rahul0805/Stair_climber/Payload Box/payload_lid.SLDPRT

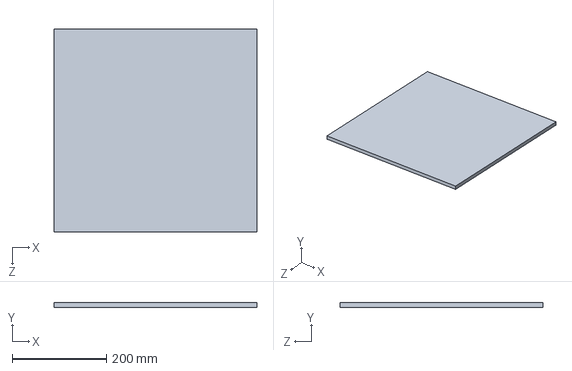
[picture p60: CAD file, 2020-08-08]
Payload Box/payload_lid.SLDPRT
430.0 x 10.0 x 430.0 mm
