rahul0805/Stair_climber/Tri Wheel/Casing/Carrier_tumble.SLDPRT

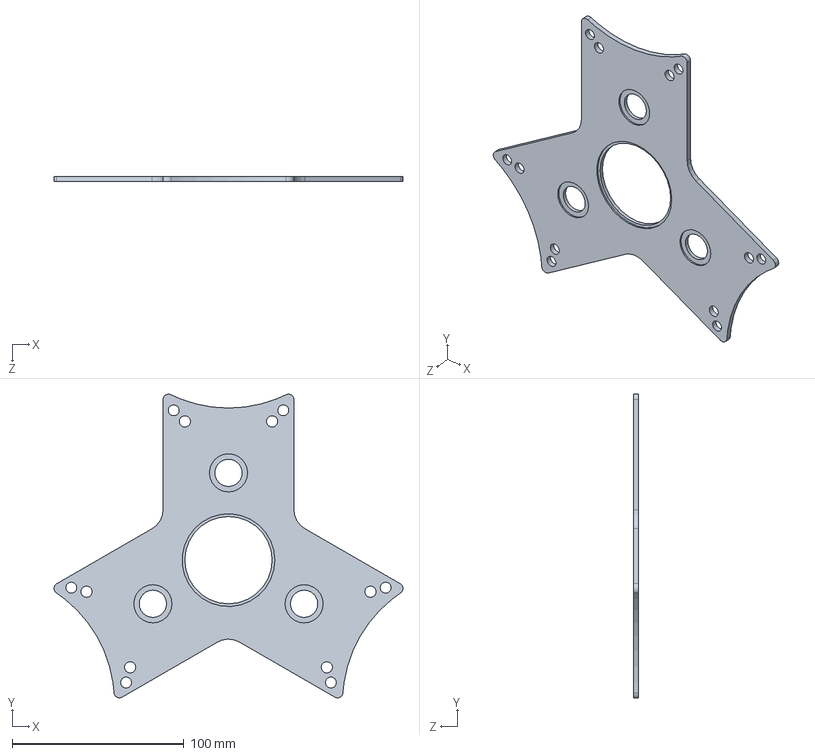
[picture p61: CAD file, 2020-08-08]
Tri Wheel/Casing/Carrier_tumble.SLDPRT
203.1 x 176.7 x 3.17 mm
