rahul0805/Stair_climber/Tri Wheel/Gears/Central & idler gears.SLDPRT

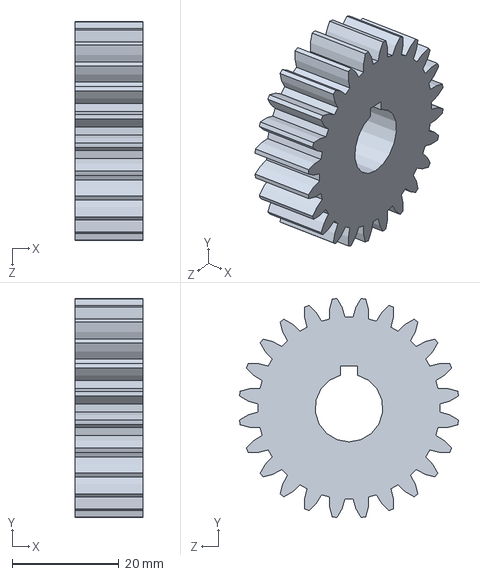
[picture p62: CAD file, 2020-08-08]
Tri Wheel/Gears/Central & idler gears.SLDPRT
12.7 x 41.0 x 41.0 mm
