rahul0805/Stair_climber/Tri Wheel/Shafts/Shaft C.SLDPRT

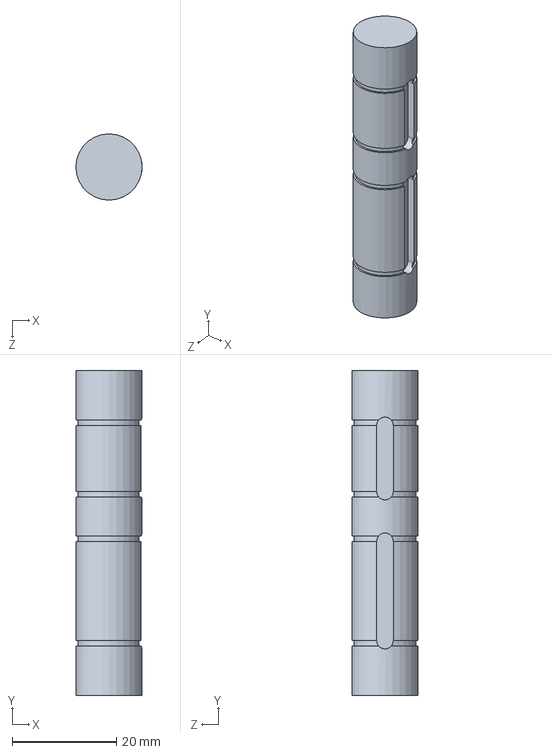
[picture p63: CAD file, 2020-08-08]
Tri Wheel/Shafts/Shaft C.SLDPRT
12.7 x 62.3 x 12.7 mm
