rahul0805/Stair_climber/Gimbal/Gimbal.stp

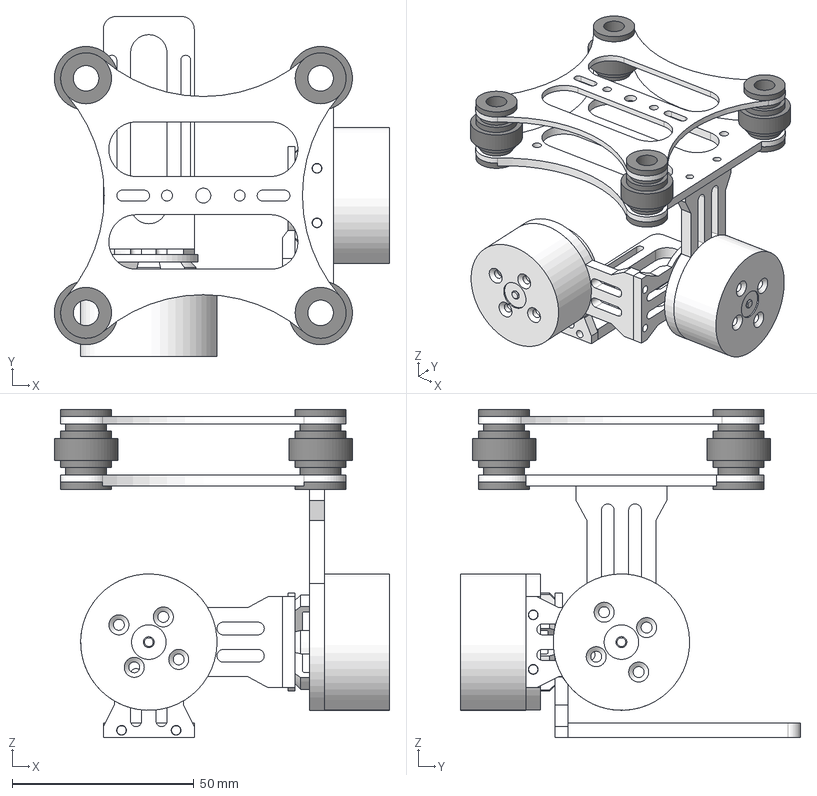
[picture p64: CAD file, 2020-08-08]
Gimbal/Gimbal.stp
92.3 x 93.5 x 90.3 mm
Top Support Plate
Rubber Spacers x 4
Bottom Support Plate
Roll Bracket
Motor
Motor Bracket x 2
Pitch Bracket
Motor - OH
Camera Support
