rahul0805/Stair_climber/Motor Assembly/midd.SLDPRT

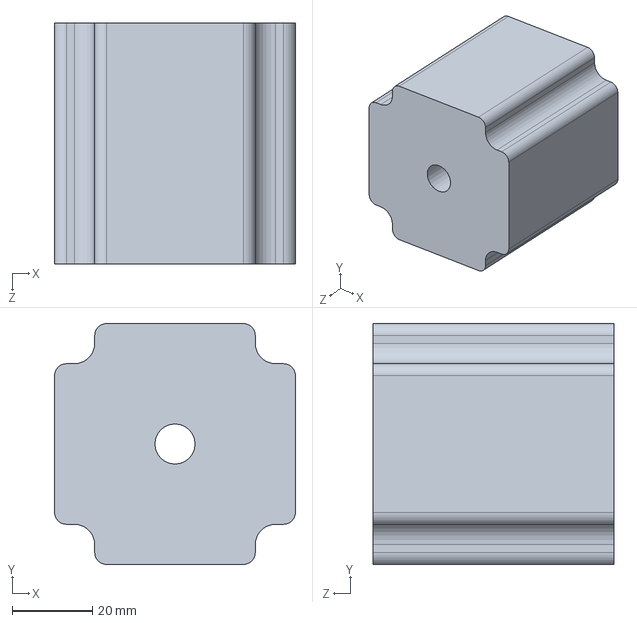
[picture p65: CAD file, 2020-08-08]
Motor Assembly/midd.SLDPRT
60.0 x 60.0 x 60.0 mm
