rahul0805/Stair_climber/Payload Box/payload_bottom.SLDPRT

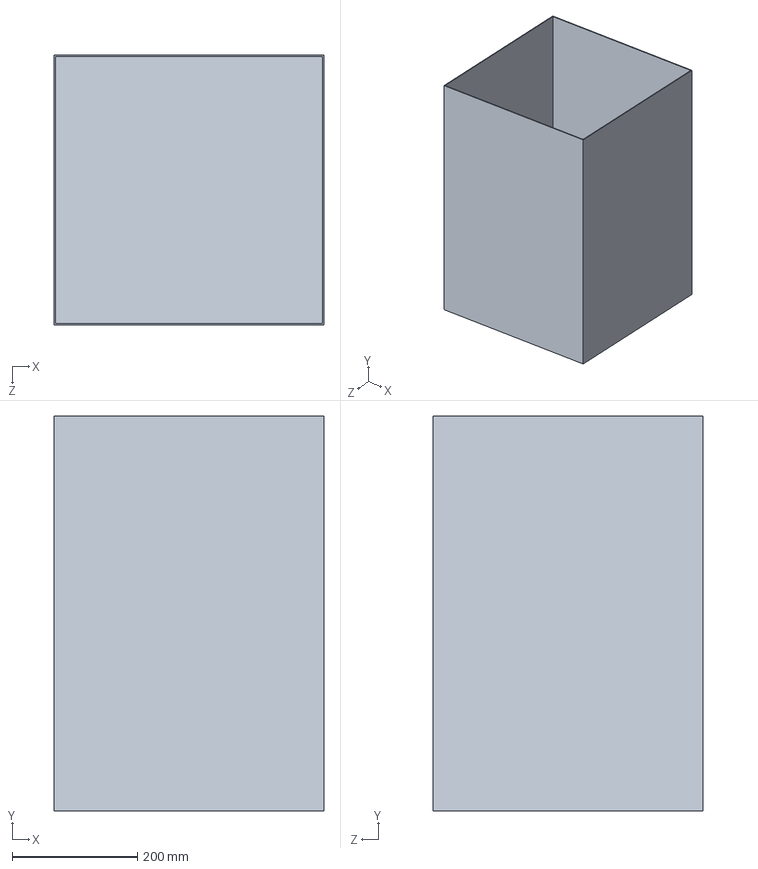
[picture p66: CAD file, 2020-08-08]
Payload Box/payload_bottom.SLDPRT
430.0 x 630.0 x 430.0 mm
