rahul0805/Stair_climber/Tri Wheel/Casing/Carrier_Drive Plate.SLDPRT

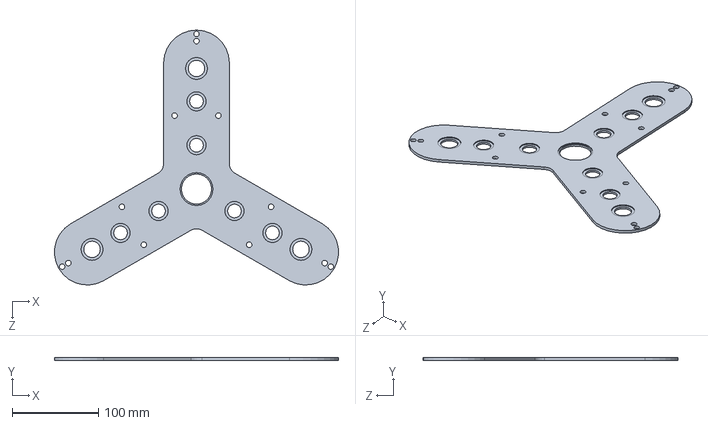
[picture p67: CAD file, 2020-08-08]
Tri Wheel/Casing/Carrier_Drive Plate.SLDPRT
329.0 x 3.17 x 295.2 mm
