rahul0805/Stair_climber/Tri Wheel/Shafts/Shaft D2.SLDPRT

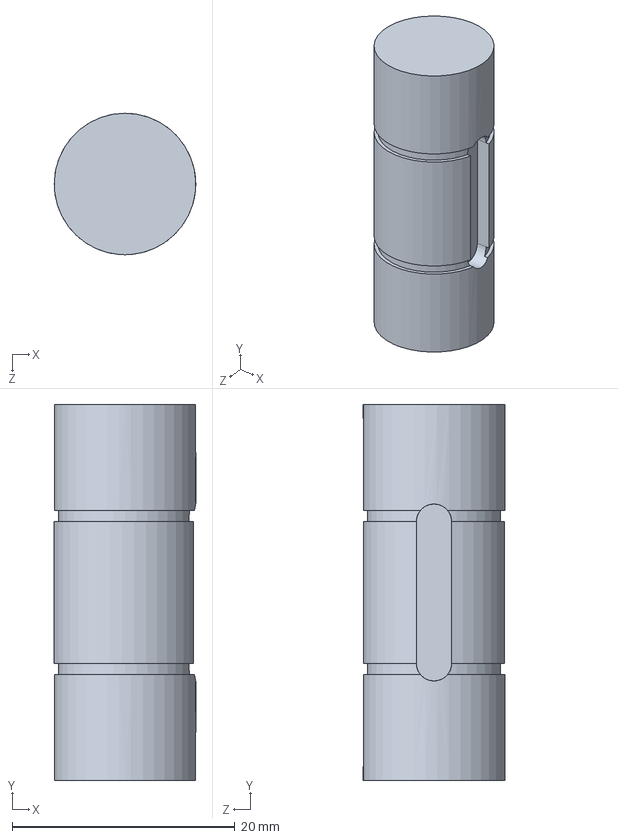
[picture p68: CAD file, 2020-08-08]
Tri Wheel/Shafts/Shaft D2.SLDPRT
12.7 x 33.7 x 12.7 mm
