rahul0805/Stair_climber/Tri Wheel/Wheels/wheel.SLDPRT

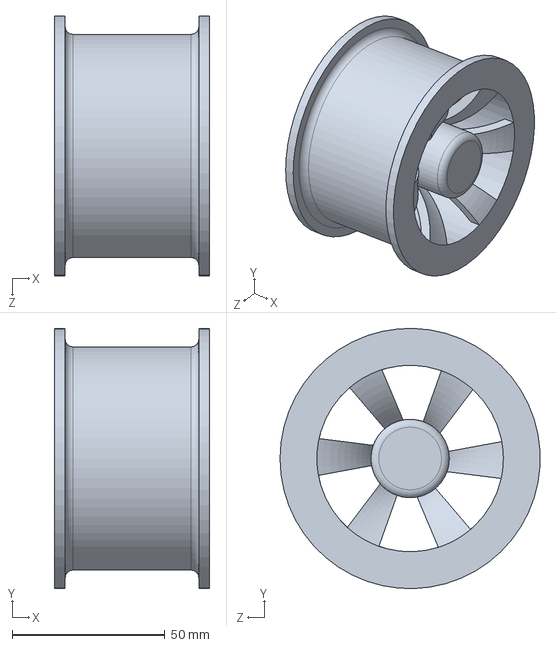
[picture p69: CAD file, 2020-08-08]
Tri Wheel/Wheels/wheel.SLDPRT
50.8 x 85.0 x 85.0 mm
