rahul0805/Stair_climber/Linear Actuator/HDA-STROKE.SLDPRT

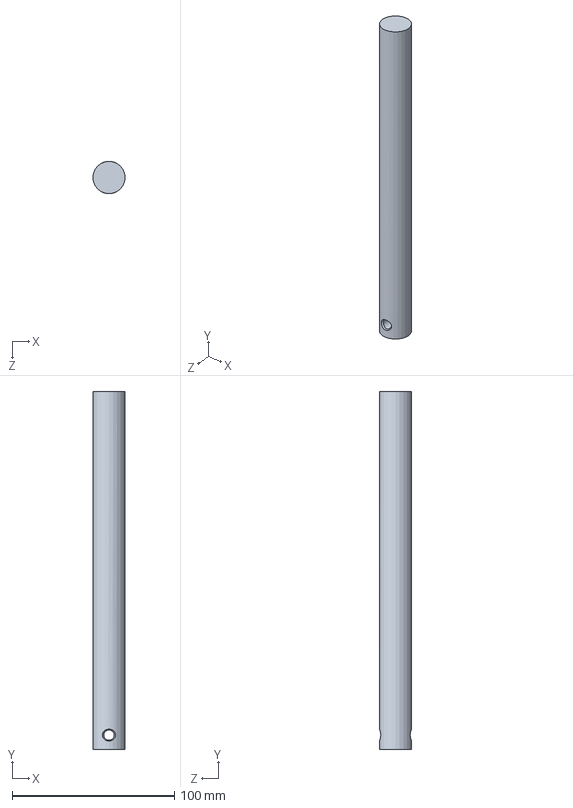
[picture p70: CAD file, 2020-08-08]
Linear Actuator/HDA-STROKE.SLDPRT
19.9 x 221.0 x 19.9 mm
