rahul0805/Stair_climber/Motor Assembly/last one.SLDPRT

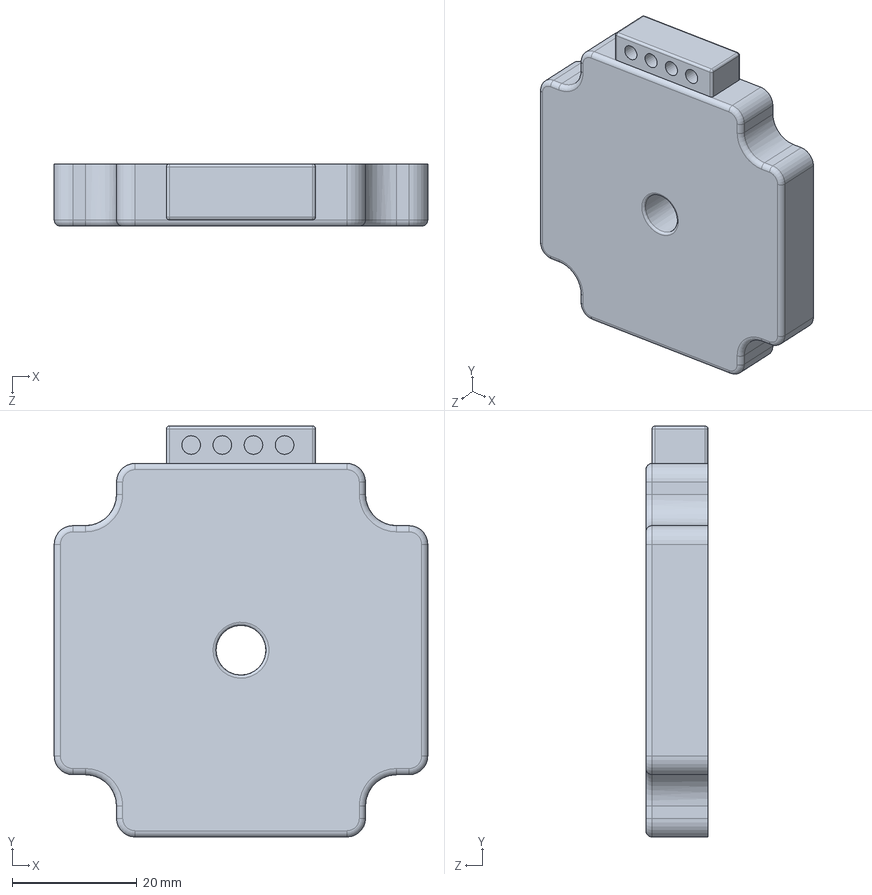
[picture p71: CAD file, 2020-08-08]
Motor Assembly/last one.SLDPRT
60.0 x 66.0 x 10.0 mm
