rahul0805/Stair_climber/Tri Wheel/Gears/Large Driving Gears.SLDPRT

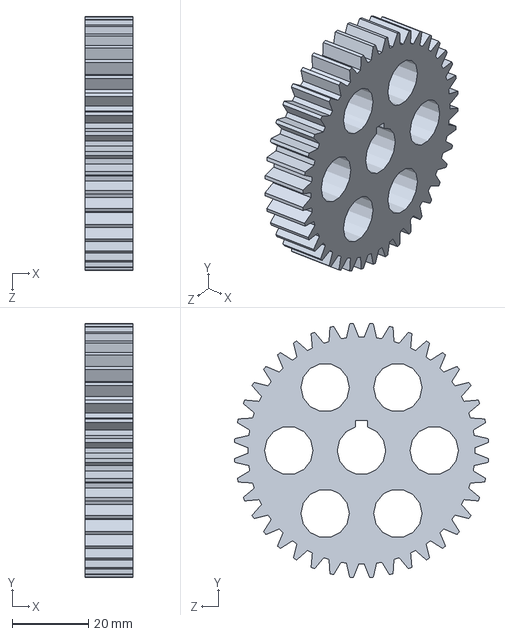
[picture p72: CAD file, 2020-08-08]
Tri Wheel/Gears/Large Driving Gears.SLDPRT
12.7 x 66.5 x 66.5 mm
