rahul0805/Stair_climber/Tri Wheel/Shafts/Shaft A.SLDPRT

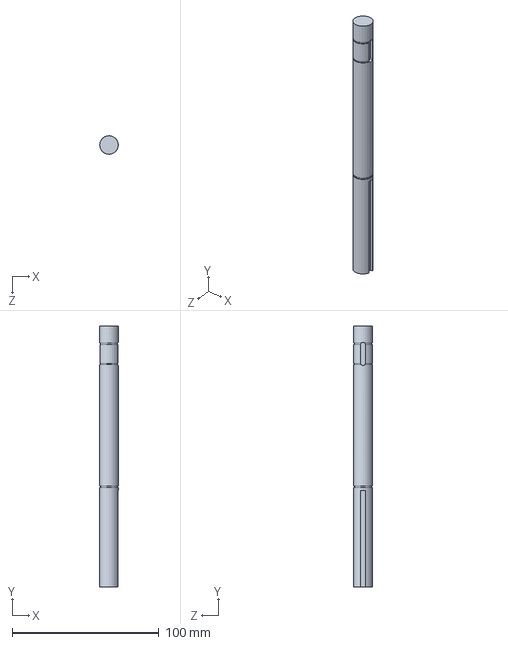
[picture p73: CAD file, 2020-08-08]
Tri Wheel/Shafts/Shaft A.SLDPRT
12.7 x 177.8 x 12.7 mm
