rahul0805/Stair_climber/Motor Assembly/one.SLDPRT

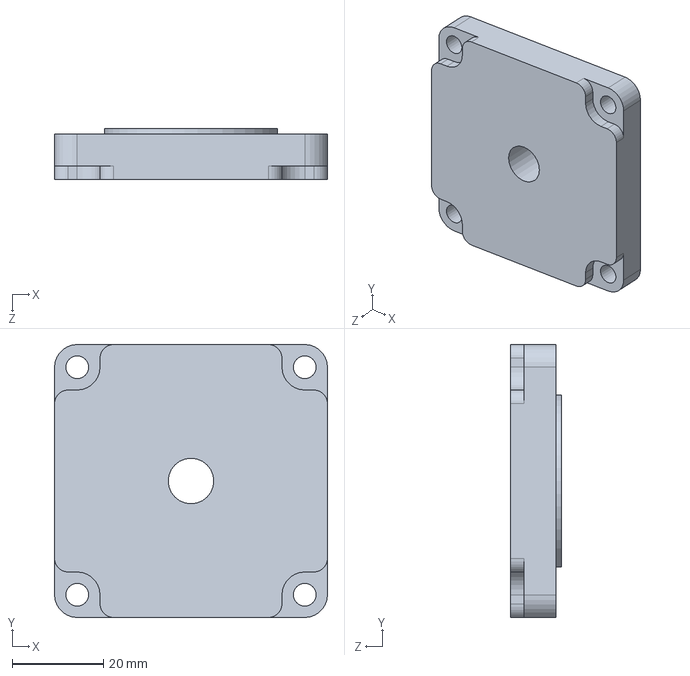
[picture p74: CAD file, 2020-08-08]
Motor Assembly/one.SLDPRT
60.0 x 60.0 x 11.2 mm
