rahul0805/Stair_climber/Tri Wheel/Gears/Small Tumbling Gears.SLDPRT

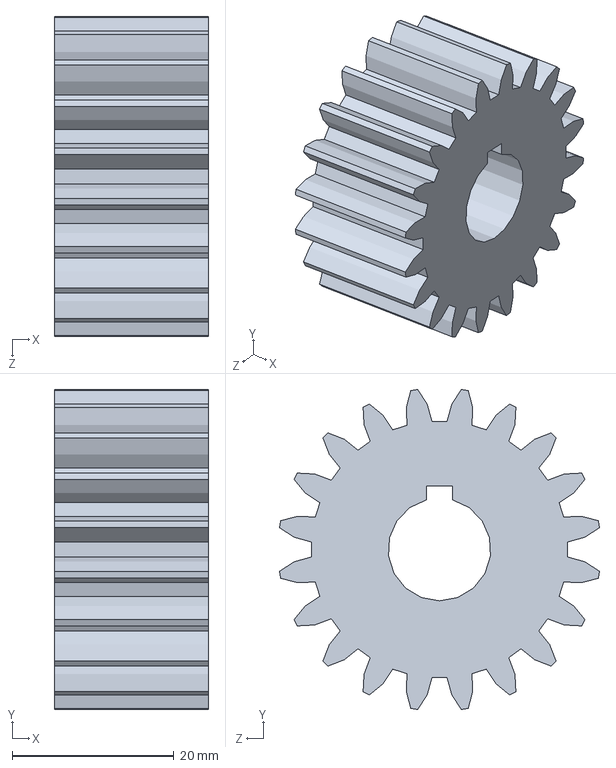
[picture p75: CAD file, 2020-08-08]
Tri Wheel/Gears/Small Tumbling Gears.SLDPRT
19.1 x 39.6 x 39.6 mm
