rahul0805/Stair_climber/Linear Actuator/HDA-SHROUD-CAP.SLDPRT

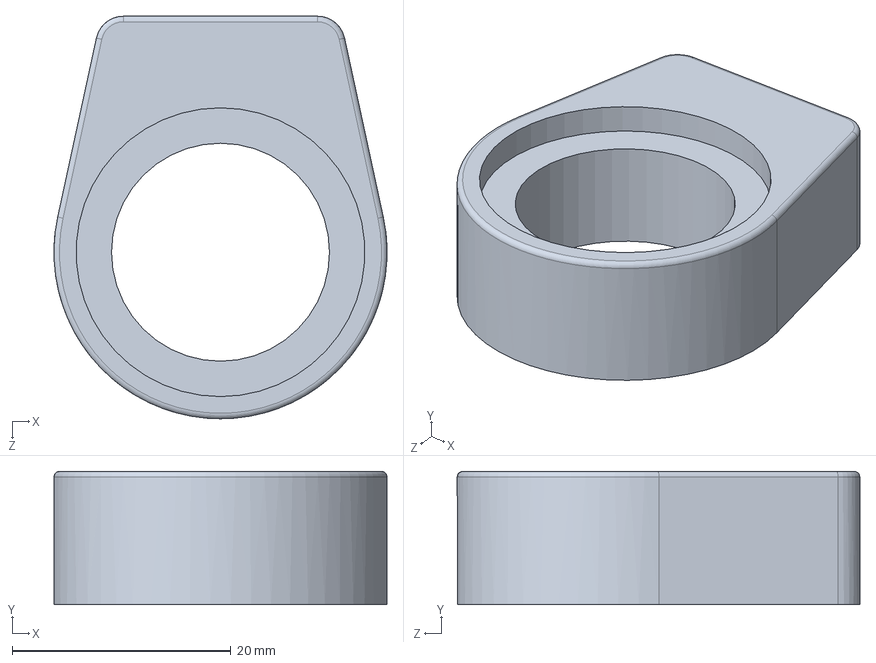
[picture p76: CAD file, 2020-08-08]
Linear Actuator/HDA-SHROUD-CAP.SLDPRT
30.5 x 12.2 x 36.8 mm
