rahul0805/Stair_climber/Linear Actuator/HDA-SHROUD.SLDPRT

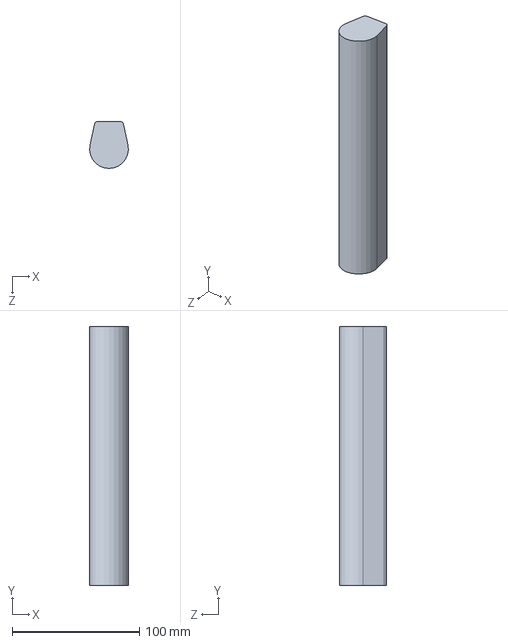
[picture p77: CAD file, 2020-08-08]
Linear Actuator/HDA-SHROUD.SLDPRT
30.5 x 203.2 x 36.8 mm
