rahul0805/Stair_climber/Linear Actuator/_test - w-celvis.STEP

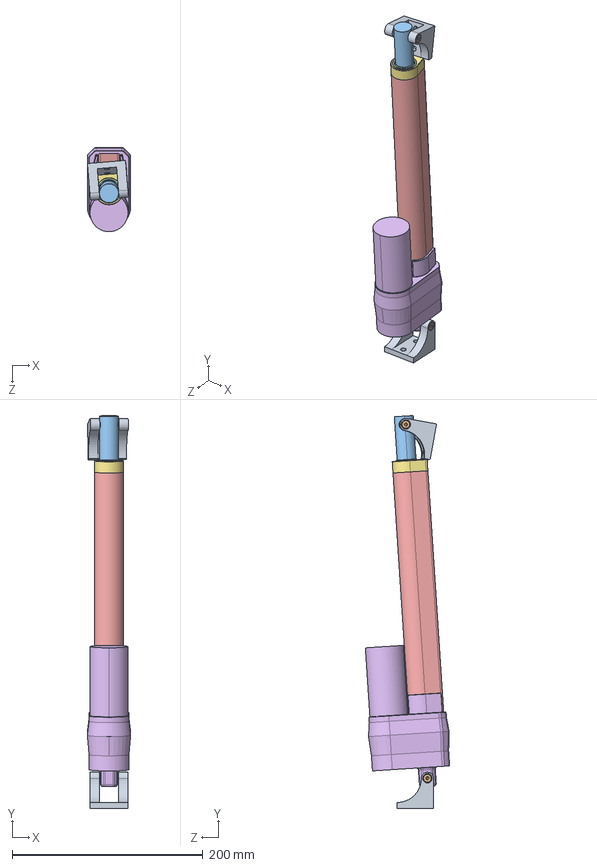
[picture p78: CAD file, 2020-08-08]
Linear Actuator/_test - w-celvis.STEP
45.5 x 412.5 x 88.5 mm
HDA Clevis Mount x 2
Shoulder Bolt .25 x 1 - 10-24_SHSSCREW 0.25x1-N x 2
HDA-STROKE_8IN
HDA-CAP-SEAL
HDA-SHROUD_8IN
HDA-BASE
HDA-SHROUD-CAP
