rahul0805/Stair_climber/Linear Actuator/HDA-BASE.SLDPRT

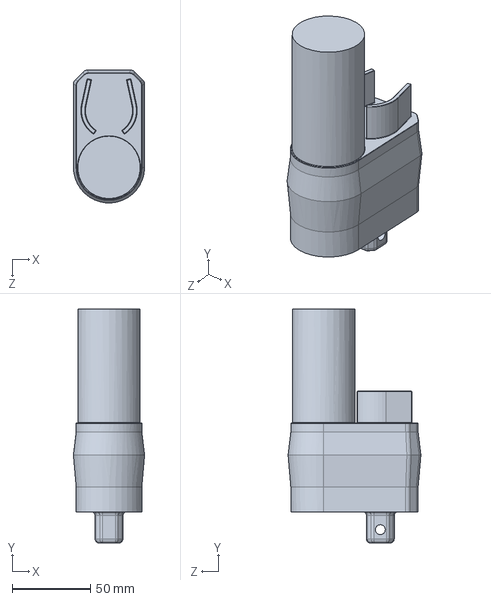
[picture p79: CAD file, 2020-08-08]
Linear Actuator/HDA-BASE.SLDPRT
45.5 x 149.4 x 84.8 mm
