rahul0805/Stair_climber/Linear Actuator/HDA Clevis Mount.SLDPRT

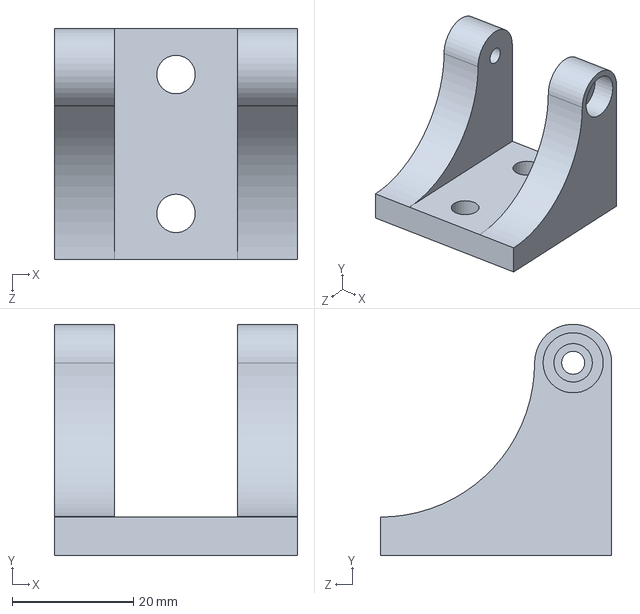
[picture p80: CAD file, 2020-08-08]
Linear Actuator/HDA Clevis Mount.SLDPRT
40.0 x 38.1 x 38.1 mm
